tomaisthorpe/embedded/humidity-monitor/hardware/board/Board/Board.kicad_sch

## KiCad design humidity-monitor/hardware/board/Board/Board.kicad_sch (2024-11-19)

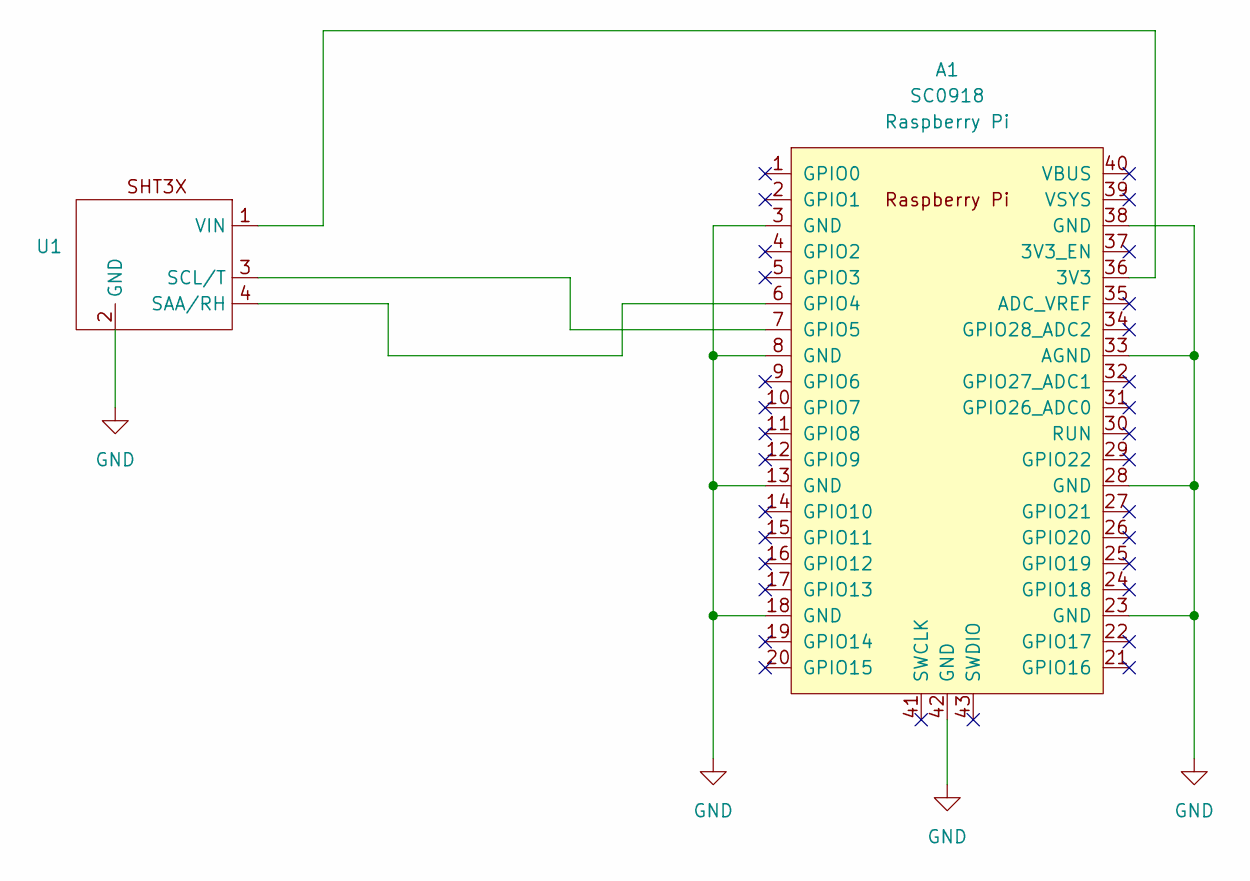
[picture p2: schematic Board.kicad_sch]

Parts:
A1: SC0918; RPi_PicoW_SMD_TH; PARTREV 1.6
U1: PinHeader_1x04_P2.54mm_Vertical

Connections:
GND: A1.3 (GND), A1.8 (GND), A1.13 (GND), A1.18 (GND), A1.23 (GND), A1.28 (GND), A1.33 (AGND), A1.38 (GND), A1.42 (GND), U1.2 (GND)
unnamed: A1.6 (GPIO4), U1.4 (SAA/RH)
unnamed: A1.7 (GPIO5), U1.3 (SCL/T)
unnamed: A1.36 (3V3), U1.1 (VIN)
